Nerdiyde/Anemosens/pictures/DSC02175.JPG

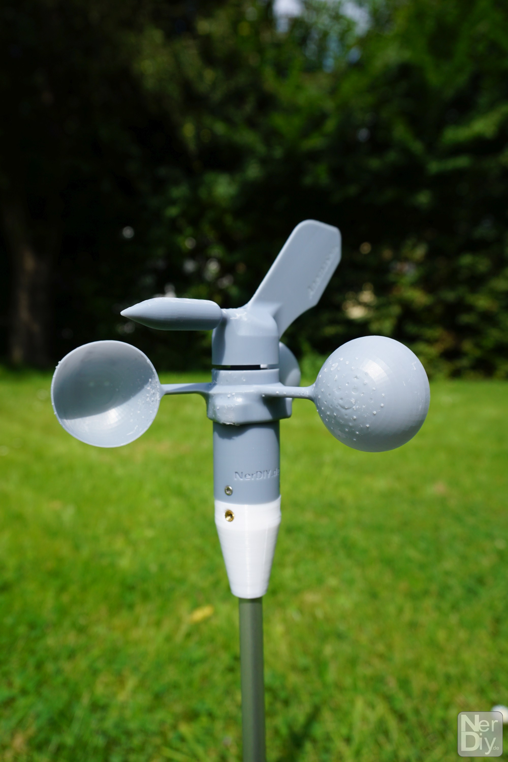
pictures/DSC02175.JPG
